ChrisDeadman/usb-to-ps2-gameport-hat/Software/usb-to-ps2-gameport-hat/include/VirtualJoystick.h

#ifndef _VIRTUAL_JOYSTICK_H_
#define _VIRTUAL_JOYSTICK_H_

#include "JoystickState.h"

class VirtualJoystick {
 private:
  JoystickState state;

 public:
  VirtualJoystick();

  /**
   * Returns the current state, then resets it.
   *
   * Deltas are summed up until pop_state is called.
   * This should be called periodically.
   */
  JoystickState pop_state();

  /**
   * Updates the current state and marks it as changed.
   *
   * Deltas are summed up until pop_state is called.
   */
  void update_state(JoystickState const* const new_state, bool is_player_1,
                    bool swap_joy_axis_3_and_4);

 private:
  void reset_state();
};

#endif  //_VIRTUAL_JOYSTICK_H_
